ISSKA/Datalogger_ISSKA/datalogger_code/notecard_datalogger/Datalogger sur le terrain/TP_22511/Tiny_IotPlotter_MS8607_MS5803_NCmos/README.md

# Description
Code for datalogger with MS8607 (PHT of air) and MS5803 (pressure and temperature of water) sensors.
The ground of the notecard is connected to the ground of the TinyPico by a transistor. The gate of this transistor is connected to pin 4.
