ISSKA/Datalogger_ISSKA/datalogger_code/notecard_datalogger/OLD_STUFF/Jsonata_expression/README.md

# JSONata
Les expressions Json sont utilisées sur notehub.io. Elles peuvent être ajoutées dans le "Routes" puis dans "Transform Data" choisir "JSONata Expression". Là on peut ajouter notre code Json pour modifier les données ou en créer de nouvelles.
