ISSKA/Datalogger_ISSKA/datalogger_code/simple_datalogger_code/OLD_STUFF/SVM41_MS8607/README.txt

Classe pour les capteurs MS8607 et le kit SVM41 à utiliser avec le main "TinyPico_datalogger.ino".
Les temps de correction sont 140 secondes pour firstRun et 125 pour les suivantes.
